tuofeichen/SmartTree-Electrical/SmartTree_Server/log.h

//#ifndef LOG_H
//#define LOG_H
//
//#include <arduino.h>
//
//void initSD();
//
//void writeLogFileHeader(char *fname);
//
//void logMeasurements(char *fname, double voltage, double CurrentIn,
//                     double CurrentOut, double Temperature, byte error);
//#endif
